madmace/ALFONSo_ICL8038/Qt/mixer.h

/*******************************************************************************

 A.L.F.O.N.S.o
 Author : Emiliano Mazza
 Version : 1.0
 Created on Date : 15/18/2020
 Last update     : 31/01/2023

 CopyRight 2006-2015 all rights are reserved

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
*******************************************************************************/

#ifndef MIXER_H
#define MIXER_H

#include <QObject>
#include <QQmlEngine>
#include "singleUnitLFOModel.h"

class Mixer : public QObject
{
    Q_OBJECT

private:

    // Singleton static instance
    static Mixer *oMixer;

    // Main Mixer Data Model
    QMap<int, SingleUnitLFOModel*> *m_mapLFOMixerModel;

    // Constructor
    explicit Mixer(QObject *parent = nullptr);
    // Mixer Destructor
    ~Mixer();

    // Save data into the model
    void updateMixerModel(quint8 byID, quint8 byType, quint8 byValue);
    // Make config JSON File from model
    void writeJSONConfig(QString sConfigJSONFile);
    // Read config JSON File to model
    void readJSONConfig(const QJsonObject ojsConfRoot);

public:

    // First initialize the instance. All classes will access via this instance
    static Mixer* getInstance();

    // Properties
    QMap<int, SingleUnitLFOModel*>* getLFOMixerModel();

    // QML singleton type provider function (callback).
    // Second, define the singleton type provider function (callback).
    static QObject *qmlInstance(QQmlEngine *engine, QJSEngine *scriptEngine);

signals:

    // Signal for update VCO enable state
    void updateVCOEnable(quint8 byID, bool isEnabled);
    // Signal for update VCO enable state
    void updateFreqSelector(quint8 byID, quint8 newValue);
    // Signal for update VCO coarse frequency
    void updateFreqCoarse(quint8 byID, quint8 newValue);
    // Signal for update VCO fine frequency
    void updateFreqFine(quint8 byID, quint8 newValue);
    // Signal for update VCO duty cycle
    void updateDutyCycle(quint8 byID, quint8 newValue);
    // Signal for update VCO harmonics switches
    void updateHarmonicsSwitches(quint8 byID, quint8 byType, bool newValue);

    // Signal for update frequency info text
    void updateFrequencyText(quint8 byID, QString sFreqText);
    // Signal for update botton panel info text
    void updateBottomInfoText(QString sInfoText);

public slots:

    // Store the status of the single control
    void setMixerValue(int iID, int iType, int iValue);

    // Load last configuration from JSON
    void loadJSONConfig(QString sConfigJSONFile);

    // Send Request for Sync All command to serial port
    void sendRequestSyncAllVCO();
    // Calcs and update VCOs frequencies
    void handleVCOFrequency(quint8 byID, quint16 uiValue);

    // Request a current VCOs frequencies
    void requestVCOFrequency(quint8 byID);
    // When requestd all ALFONSo application is under shutdown
    void requestALFONSoUnderClosing();

};

#endif // MIXER_H
