madmace/ALFONSo_ICL8038/Qt/serialPort.h

/*******************************************************************************

 A.L.F.O.N.S.o
 Author : Emiliano Mazza
 Version : 1.0
 Created on Date : 15/18/2020
 Last update     : 31/01/2023

 CopyRight 2006-2015 all rights are reserved

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
*******************************************************************************/

#ifndef SERIALPORT_H
#define SERIALPORT_H

#include <QObject>
#include <QSerialPort>
#include <QSerialPortInfo>
#include <QTimer>

class SerialPort : public QObject
{
    Q_OBJECT
    Q_PROPERTY(bool isSerialPortOpen READ isSerialPortOpen CONSTANT)

public:

    // Constructor
    explicit SerialPort(QObject *parent = nullptr);

    // Gets Properties
    bool isSerialPortOpen();

private:

    // ALFONSo Serial Port Name in use
    QString m_sSerialPortName;
    // True if is port open
    bool m_bSerialPortOpen;
    // ALFONSo Serial Port
    QSerialPort* m_oSerial = nullptr;
    // Timer for check if Serial Port present
    QTimer* m_oCheckSerialTimer = nullptr;

    // Return to the USB Serial ALFONSo if is present
    QString getALFONSoUSB();

signals:

    // Signal containing available serial ports
    void availablePortsWorker(QList<QSerialPortInfo> lPorts);
    // Signal if ALFONSo device is present or not
    void isALFONSoUSBPresentWorker(bool bResult);
    // Signal for receive data from serial port
    void receivedBytesWorker(const QByteArray &data);

private slots:

    // Receive data from serial port
    void handleReceiveBytesWorker();
    // Check if the USB Serial ALFONSo if is available
    void handleIsAvailableALFONSoUSB();

public slots:

    // Get All available Serial Ports
    void handleAvailablePortsWorker();
    // Return true if USB Serial ALFONSo is present, otherwise false
    void handleIsALFONSoUSBPresentWorker();
    // Perform all Serial Port operation for close ALFONSo
    void handleALFONSoUnderClosingWorker();

    // Send data to serial port
    void handleSendBytesWorker(const QByteArray &data);

};

#endif // SERIALPORT_H
